Mrszcup/jetson-nano-baseboard/display.sch

## KiCad design display.sch (2021-12-20)

Schematic: display.sch

Parts:
C1, C2: C_4u7_0402; 0402-cap; MPN GRM155R61A475MEAAD
C26, C27, C73, C74, C75, C76, C77, C78, C79, C80: C_100n_0402; 0402-cap; MPN 0402X104K6R3CT
D4: 1N4148WS; SOD-323; MPN 1N4148WS
IC6: PCA9517ADP; MSOP-8; MPN PCA9517ADP
IC18: SON-15; PartSymbol TPD8S009DSMR
J1: 46756-1001; HDMI_Micro-D_Molex_46765-1x01; MPN 467651001
L8, L9: BLM18SG121TN1D; 0603; MPN BLM18SG121TN1D
M1: jetson-nano-connector; PartSymbol 2309413-1
R1, R2, R3, R4, R7, R8, R9, R10: R_5R6_0402; 0402-res; MPN ERJ2GEJ5R6X
R5, R6, R11, R37, R81, R83, R88: R_2k_0402; 0402-res; MPN CRCW04022K00FKED
R12, R82, R98, R99: R_0R_0402; 0402-res; MPN ERJ2GE0R00X
T1: BSS138APW; SC70-3; MPN BSS138PW
TP2, TP25, TP26, TP33, TP34, TP35, TP36: TP-R-1.5; MPN N/A
U6, U7: TPD4E05U06QDQARQ1; MPN TPD4E05U06QDQARQ1

Connections:
1V8_SYS: R88.1
3V3_SYS: C26.1, IC6.1 (VCCA), R11.1, R81.1
5V0_SYS: L9.1
DP_HDP: M1.88 (DP0_HPD)
EDP0_TX_N: M1.39 (DP0_TXD0_N)
EDP0_TX_P: M1.41 (DP0_TXD0_P)
EDP1_TX_N: M1.45 (DP0_TXD1_N)
EDP1_TX_P: M1.47 (DP0_TXD1_P)
EDP2_TX_N: M1.51 (DP0_TXD2_N)
EDP2_TX_P: M1.53 (DP0_TXD2_P)
EDP3_TX_N: M1.57 (DP0_TXD3_N)
EDP3_TX_P: M1.59 (DP0_TXD3_P)
EDP_AUX_N: M1.90 (DP0_AUX_N)
EDP_AUX_P: M1.92 (DP0_AUX_P)
GND: C1.1, C2.1, C26.2, C27.1, IC6.4 (GND), IC18.2 (GND), IC18.5 (GND), IC18.8 (GND), IC18.11 (GND), L8.1, R12.1, R37.2, R83.2, T1.2 (S), U6.3 (GND), U6.8 (GND), U7.3 (GND), U7.8 (GND)
HDMI_PWR: C27.2, D4.A, IC6.5 (EN), IC6.8 (VCCB), IC18.13 (VCC), IC18.15 (VCC), L9.2, R5.1, R6.1
HDMI_SHIELD: J1.4 (D2S), J1.7 (D1S), J1.10 (D0S), J1.13 (CKS), J1.SH, L8.2
M2_ALERT: M1.212 (GPIO10), TP2.1
unnamed: C1.2, C2.2, D4.C, J1.19 (+5V)
unnamed: IC6.2 (SCLA), R81.2, R98.1
unnamed: IC6.3 (SDAA), R11.2, R99.1
unnamed: R82.2, R83.1, T1.1 (G)
unnamed: U6.4 (IO3), U6.7 (IO3)
unnamed: U6.5 (IO4), U6.6 (IO4)
unnamed: U7.5 (IO4), U7.6 (IO4)
OTG_USB_VBUS: M1.87 (GPIO00)
TMDS_C1_CLK_N: C80.2, IC18.12 (D3-), R10.1
TMDS_C1_CLK_P: C78.2, IC18.10 (D3+), R9.1
TMDS_C1_D0_N: C79.2, IC18.9 (D2-), R8.1
TMDS_C1_D0_P: C76.2, IC18.7 (D2+), R7.1
TMDS_C1_D1_N: C77.2, IC18.6 (D1-), R4.1
TMDS_C1_D1_P: C75.2, IC18.4 (D1+), R3.1
TMDS_C1_D2_N: C74.2, IC18.3 (D0-), R2.1
TMDS_C1_D2_P: C73.2, IC18.1 (D0+), R1.1
TMDS_CEC: M1.94 (HDMI_CEC), TP26.1
TMDS_CEC_GND: J1.16 (GND), R12.2, U6.2 (IO2), U6.9 (IO2)
TMDS_CEC_IN: J1.15 (CEC), R37.1, U6.1 (IO1), U6.10 (IO1)
TMDS_CLK_C_N: J1.14 (CK-), R10.2
TMDS_CLK_C_P: J1.12 (CK+), R9.2
TMDS_CLK_N: C80.1, M1.81 (DP1_TXD3_N)
TMDS_CLK_P: C78.1, M1.83 (DP1_TXD3_P)
TMDS_D0_C_N: J1.11 (D0-), R8.2
TMDS_D0_C_P: J1.9 (D0+), R7.2
TMDS_D0_N: C79.1, M1.75 (DP1_TXD2_N)
TMDS_D0_P: C76.1, M1.77 (DP1_TXD2_P)
TMDS_D1_C_N: J1.8 (D1-), R4.2
TMDS_D1_C_P: J1.6 (D1+), R3.2
TMDS_D1_N: C77.1, M1.69 (DP1_TXD1_N)
TMDS_D1_P: C75.1, M1.71 (DP1_TXD1_P)
TMDS_D2_C_N: J1.5 (D2-), R2.2
TMDS_D2_C_P: J1.3 (D2+), R1.2
TMDS_D2_N: C74.1, M1.63 (DP1_TXD0_N)
TMDS_D2_P: C73.1, M1.65 (DP1_TXD0_P)
TMDS_HPD: M1.96 (DP1_HPD), R88.2, T1.3 (D), TP25.1
TMDS_HPD_IN: J1.1 (HPD/HEAC-), R82.1, U7.4 (IO3), U7.7 (IO3)
TMDS_SCL: M1.100 (DP1_AUX_P), R98.2, TP33.1
TMDS_SCL_5V0: IC6.7 (SCLB), J1.17 (SCL), R5.2, U7.2 (IO2), U7.9 (IO2)
TMDS_SDA: M1.98 (DP1_AUX_N), R99.2, TP34.1
TMDS_SDA_5V0: IC6.6 (SDAB), J1.18 (SDA), R6.2, U7.1 (IO1), U7.10 (IO1)
USR_BUTTON: M1.218 (GPIO12), TP36.1
USR_LED: M1.206 (GPIO07), TP35.1

Notes on the sheet:
Text
Display
1V8
HDMI Interface
DDC/HPD
3V3
5V0
