Mrszcup/jetson-nano-baseboard/id-serial.sch

## KiCad design id-serial.sch (2021-12-31)

Schematic: id-serial.sch

Parts:
C36: C_100n_0402; 0402-cap; MPN 0402X104K6R3CT
D15: diode; SOD-323; MPN 1N4148WS
IC17: AT24CS01-ST; SOT23-5; MPN AT24CS01-ST
R132: R_0R_0402; 0402-res; MPN ERJ2GE0R00X
TP30: TC2030; MPN TC2030

Connections:
3V3_SYS: C36.2, D15.A
EEPROM_PWR: D15.C, IC17.4 (VCC), TP30.1 (VCC/VCCIO)
GEN0_SCL: IC17.1 (SCL), TP30.4 (TXD/TCLK)
GEN0_SDA: IC17.3 (SDA), TP30.3 (RXD/TDI), TP30.6 (RTS/TDO)
GND: C36.1, IC17.2 (GND), TP30.5 (GND)
unnamed: R132.2, TP30.2 (CTS/TMS)
SN_WP: IC17.5 (WP), R132.1

Notes on the sheet:
Text
EEPROM with Unique ID
0x58h - SN
I2C address:
0x50h - memory
ID serial
