Mrszcup/jetson-nano-baseboard/interfaces.sch

## KiCad design interfaces.sch (2021-12-21)

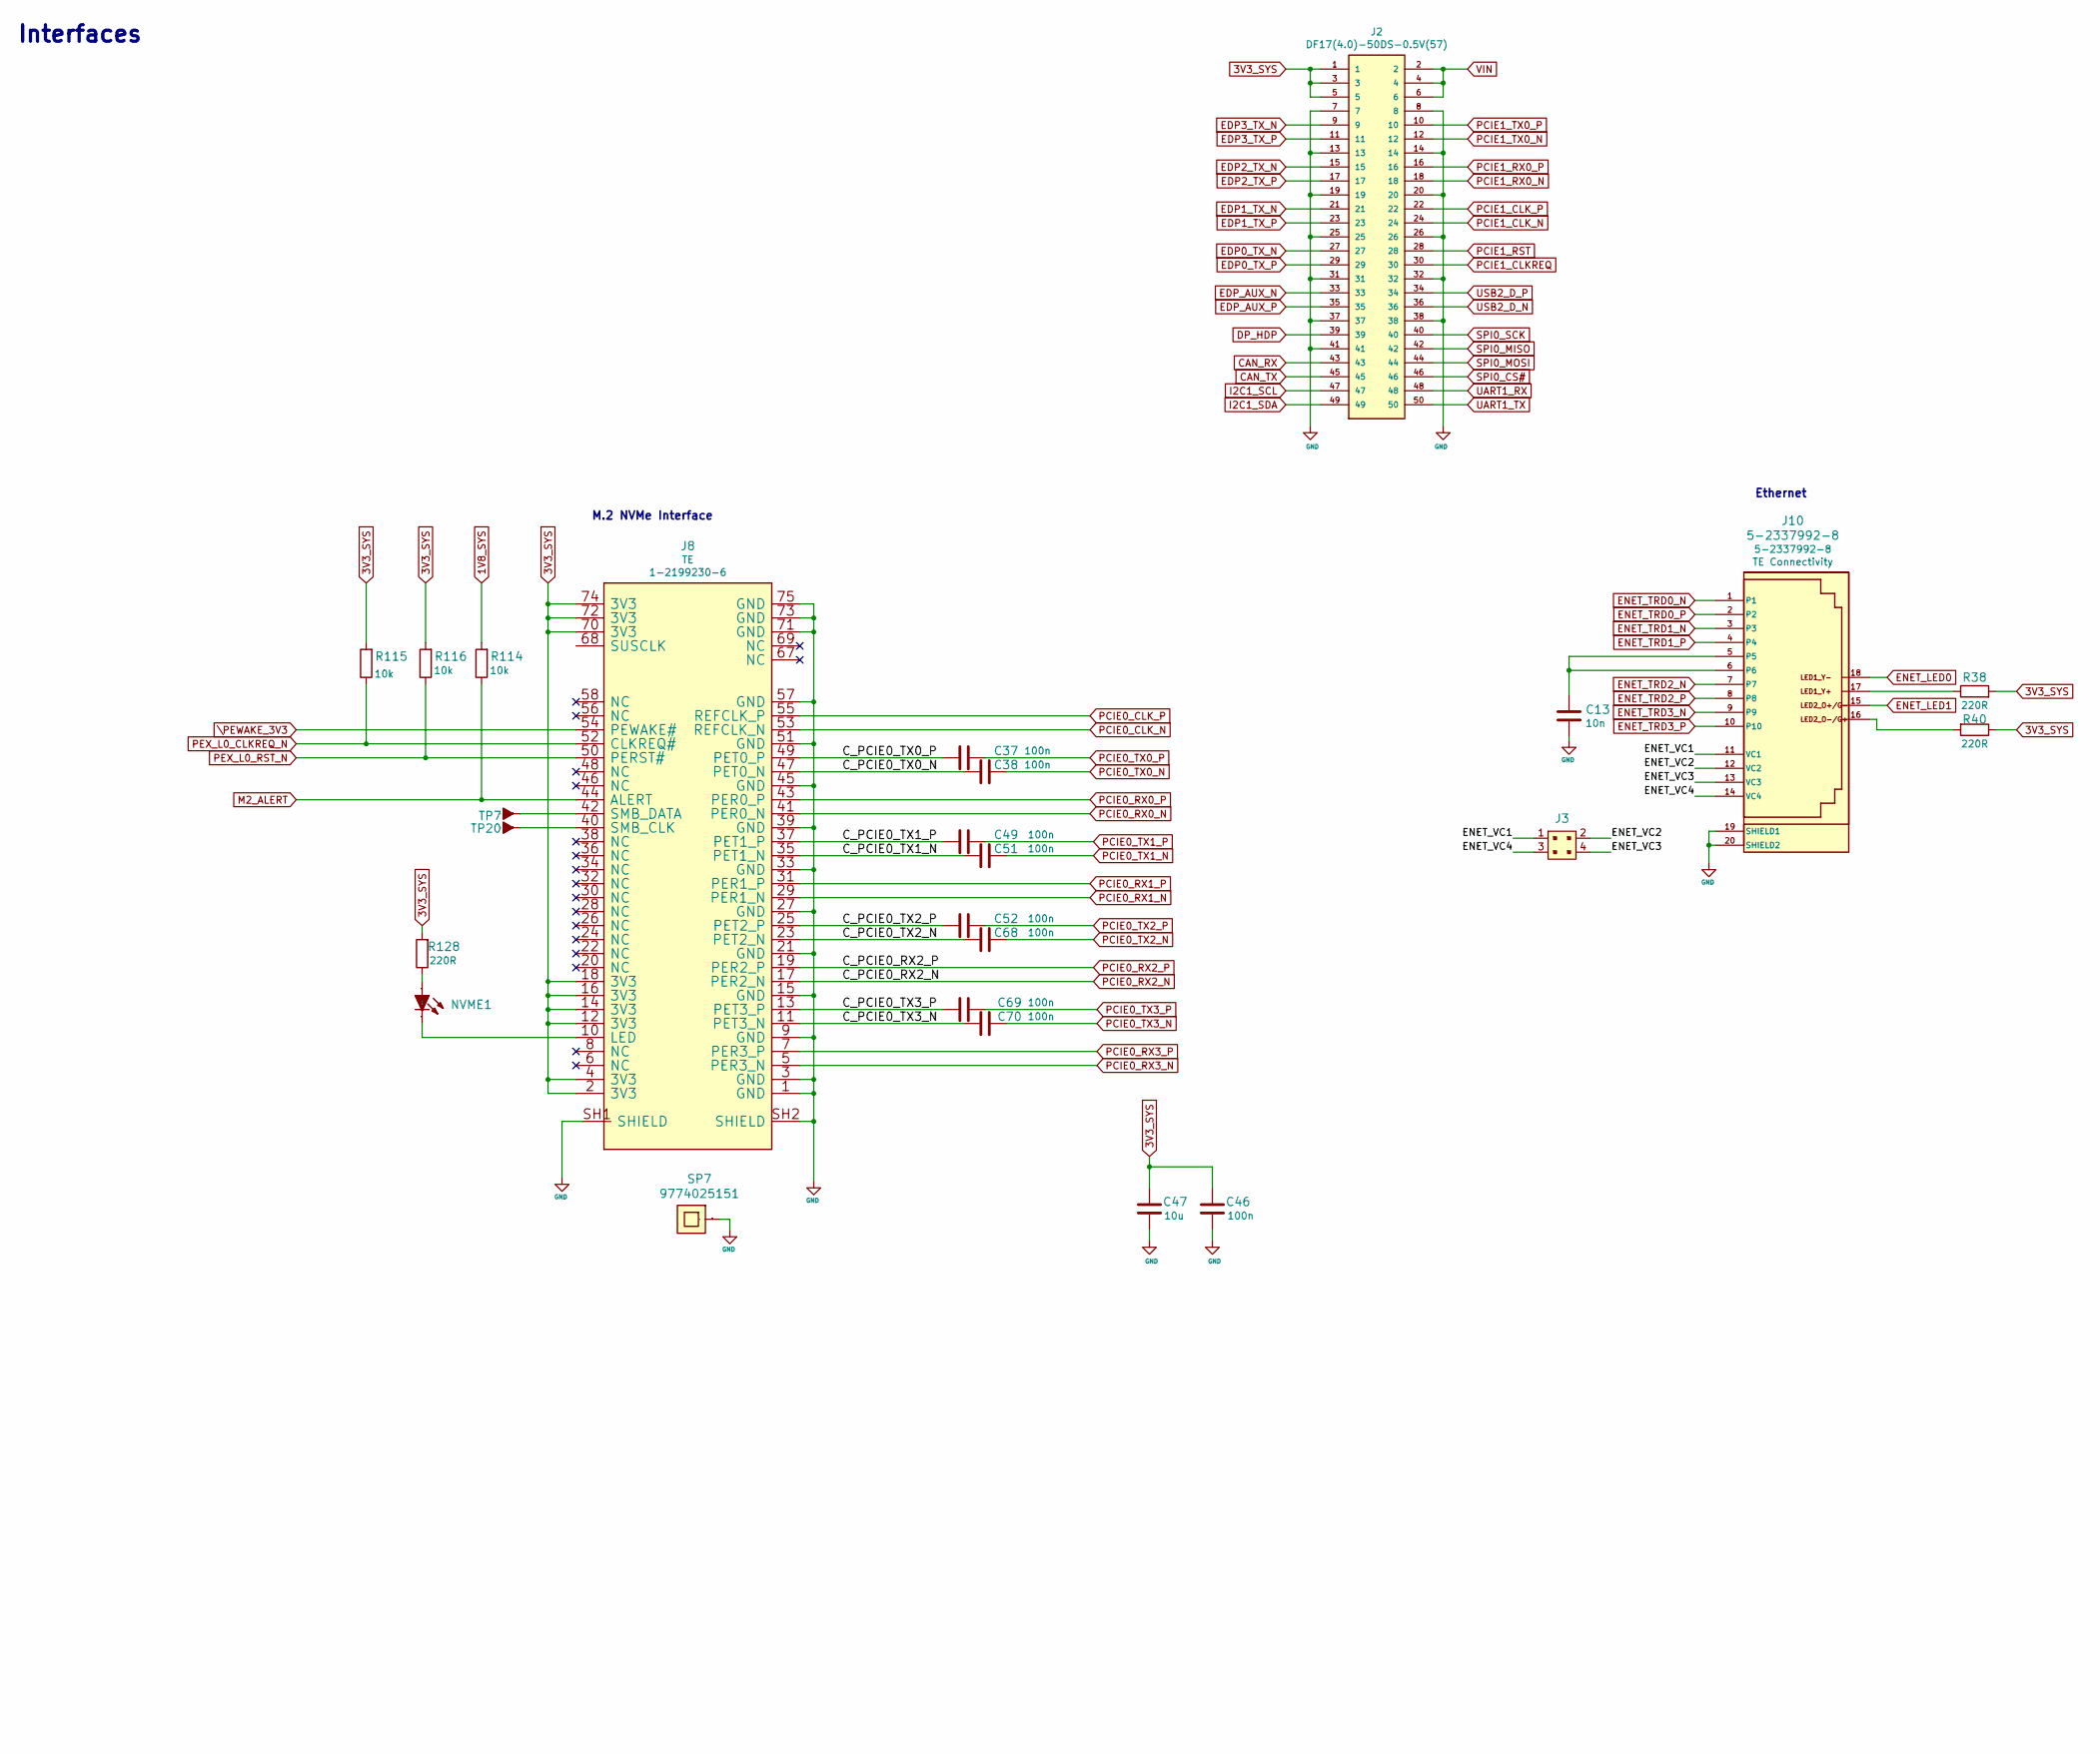
[picture p3: schematic interfaces.sch, part in row 1, column 1]

Parts:
C13: C_10n_0402; 0402-cap; MPN 04025G103ZAT2A
C37, C38, C46, C49, C51, C52, C68, C69, C70: C_100n_0402; 0402-cap; MPN 0402X104K6R3CT
C47: C_10u_0603; 0603-cap; MPN GRM188R61A106KE69D
J2: DF17(4.0)-50DS-0.5V(57); HRS_DF17(4.0)-50DS-0.5V(57); MPN DF17(4.0)-50DS-0.5V(57)
J3: 62100421821; 621304242921; MPN 62100421821
J8: 1-2199230-6; MPN 1-2199230-6
J10: 5-2337992-8; MPN 5-2337992-8
NVME1: LED0603; MPN KPT-1608SGC
R38, R40, R128: R_220R_0402; 0402-res; MPN ERJ2GEJ221X
R114, R115, R116: R_10k_0402; 0402-res; MPN CRCW040210K0FKEDHP
SP7: 9774025151; MPN 9774025151
TP7, TP20: TP-R-1.5; MPN N/A

Connections:
1V8_SYS: R114.2
3V3_SYS: C46.2, C47.2, J2.1, J2.3, J2.5, J8.2 (3V3), J8.4 (3V3), J8.12 (3V3), J8.14 (3V3), J8.16 (3V3), J8.18 (3V3), J8.70 (3V3), J8.72 (3V3), J8.74 (3V3), R38.2, R40.1, R115.2, R116.2, R128.2
CAN_RX: J2.43
CAN_TX: J2.45
C_PCIE0_TX0_N: C38.1, J8.47 (PET0_N)
C_PCIE0_TX0_P: C37.1, J8.49 (PET0_P)
C_PCIE0_TX1_N: C51.1, J8.35 (PET1_N)
C_PCIE0_TX1_P: C49.1, J8.37 (PET1_P)
C_PCIE0_TX2_N: C68.1, J8.23 (PET2_N)
C_PCIE0_TX2_P: C52.1, J8.25 (PET2_P)
C_PCIE0_TX3_N: C70.1, J8.11 (PET3_N)
C_PCIE0_TX3_P: C69.1, J8.13 (PET3_P)
DP_HDP: J2.39
EDP0_TX_N: J2.27
EDP0_TX_P: J2.29
EDP1_TX_N: J2.21
EDP1_TX_P: J2.23
EDP2_TX_N: J2.15
EDP2_TX_P: J2.17
EDP3_TX_N: J2.9
EDP3_TX_P: J2.11
EDP_AUX_N: J2.33
EDP_AUX_P: J2.35
ENET_LED0: J10.18
ENET_LED1: J10.15
ENET_TRD0_N: J10.1
ENET_TRD0_P: J10.2
ENET_TRD1_N: J10.3
ENET_TRD1_P: J10.4
ENET_TRD2_N: J10.7
ENET_TRD2_P: J10.8
ENET_TRD3_N: J10.9
ENET_TRD3_P: J10.10
ENET_VC1: J3.1, J10.11 (VC1)
ENET_VC2: J3.2, J10.12 (VC2)
ENET_VC3: J3.4, J10.13 (VC3)
ENET_VC4: J3.3, J10.14 (VC4)
GND: C13.2, C46.1, C47.1, J2.7, J2.8, J2.13, J2.14, J2.19, J2.20, J2.25, J2.26, J2.31, J2.32, J2.37, J2.38, J2.41, J8.1 (GND), J8.3 (GND), J8.9 (GND), J8.15 (GND), J8.21 (GND), J8.27 (GND), J8.33 (GND), J8.39 (GND), J8.45 (GND), J8.51 (GND), J8.57 (GND), J8.71 (GND), J8.73 (GND), J8.75 (GND), J8.SH1 (SHIELD), J8.SH2 (SHIELD), J10.19 (SHIELD1), J10.20 (SHIELD2), SP7.1
I2C1_SCL: J2.47
I2C1_SDA: J2.49
M2_ALERT: J8.44 (ALERT), R114.1
unnamed: C13.1, J10.5, J10.6
unnamed: J8.10 (LED), NVME1.K
unnamed: J8.40 (SMB_CLK), TP20.1
unnamed: J8.42 (SMB_DATA), TP7.1
unnamed: J10.16, R40.2
unnamed: J10.17, R38.1
unnamed: NVME1.A, R128.1
PCIE0_CLK_N: J8.53 (REFCLK_N)
PCIE0_CLK_P: J8.55 (REFCLK_P)
PCIE0_RX0_N: J8.41 (PER0_N)
PCIE0_RX0_P: J8.43 (PER0_P)
PCIE0_RX1_N: J8.29 (PER1_N)
PCIE0_RX1_P: J8.31 (PER1_P)
PCIE0_RX2_N: J8.17 (PER2_N)
PCIE0_RX2_P: J8.19 (PER2_P)
PCIE0_RX3_N: J8.5 (PER3_N)
PCIE0_RX3_P: J8.7 (PER3_P)
PCIE0_TX0_N: C38.2
PCIE0_TX0_P: C37.2
PCIE0_TX1_N: C51.2
PCIE0_TX1_P: C49.2
PCIE0_TX2_N: C68.2
PCIE0_TX2_P: C52.2
PCIE0_TX3_N: C70.2
PCIE0_TX3_P: C69.2
PCIE1_CLKREQ: J2.30
PCIE1_CLK_N: J2.24
PCIE1_CLK_P: J2.22
PCIE1_RST: J2.28
PCIE1_RX0_N: J2.18
PCIE1_RX0_P: J2.16
PCIE1_TX0_N: J2.12
PCIE1_TX0_P: J2.10
PEX_L0_CLKREQ_N: J8.52 (CLKREQ#), R115.1
PEX_L0_RST_N: J8.50 (PERST#), R116.1
SPI0_CS#: J2.46
SPI0_MISO: J2.42
SPI0_MOSI: J2.44
SPI0_SCK: J2.40
UART1_RX: J2.48
UART1_TX: J2.50
USB2_D_N: J2.36
USB2_D_P: J2.34
VIN: J2.2, J2.4, J2.6
\PEWAKE_3V3: J8.54 (PEWAKE#)

Notes on the sheet:
Text
Ethernet
M.2 NVMe Interface
Interfaces
