Mrszcup/jetson-nano-baseboard/jetson-nano-baseboard.sch

## KiCad design jetson-nano-baseboard.sch (2021-10-04)

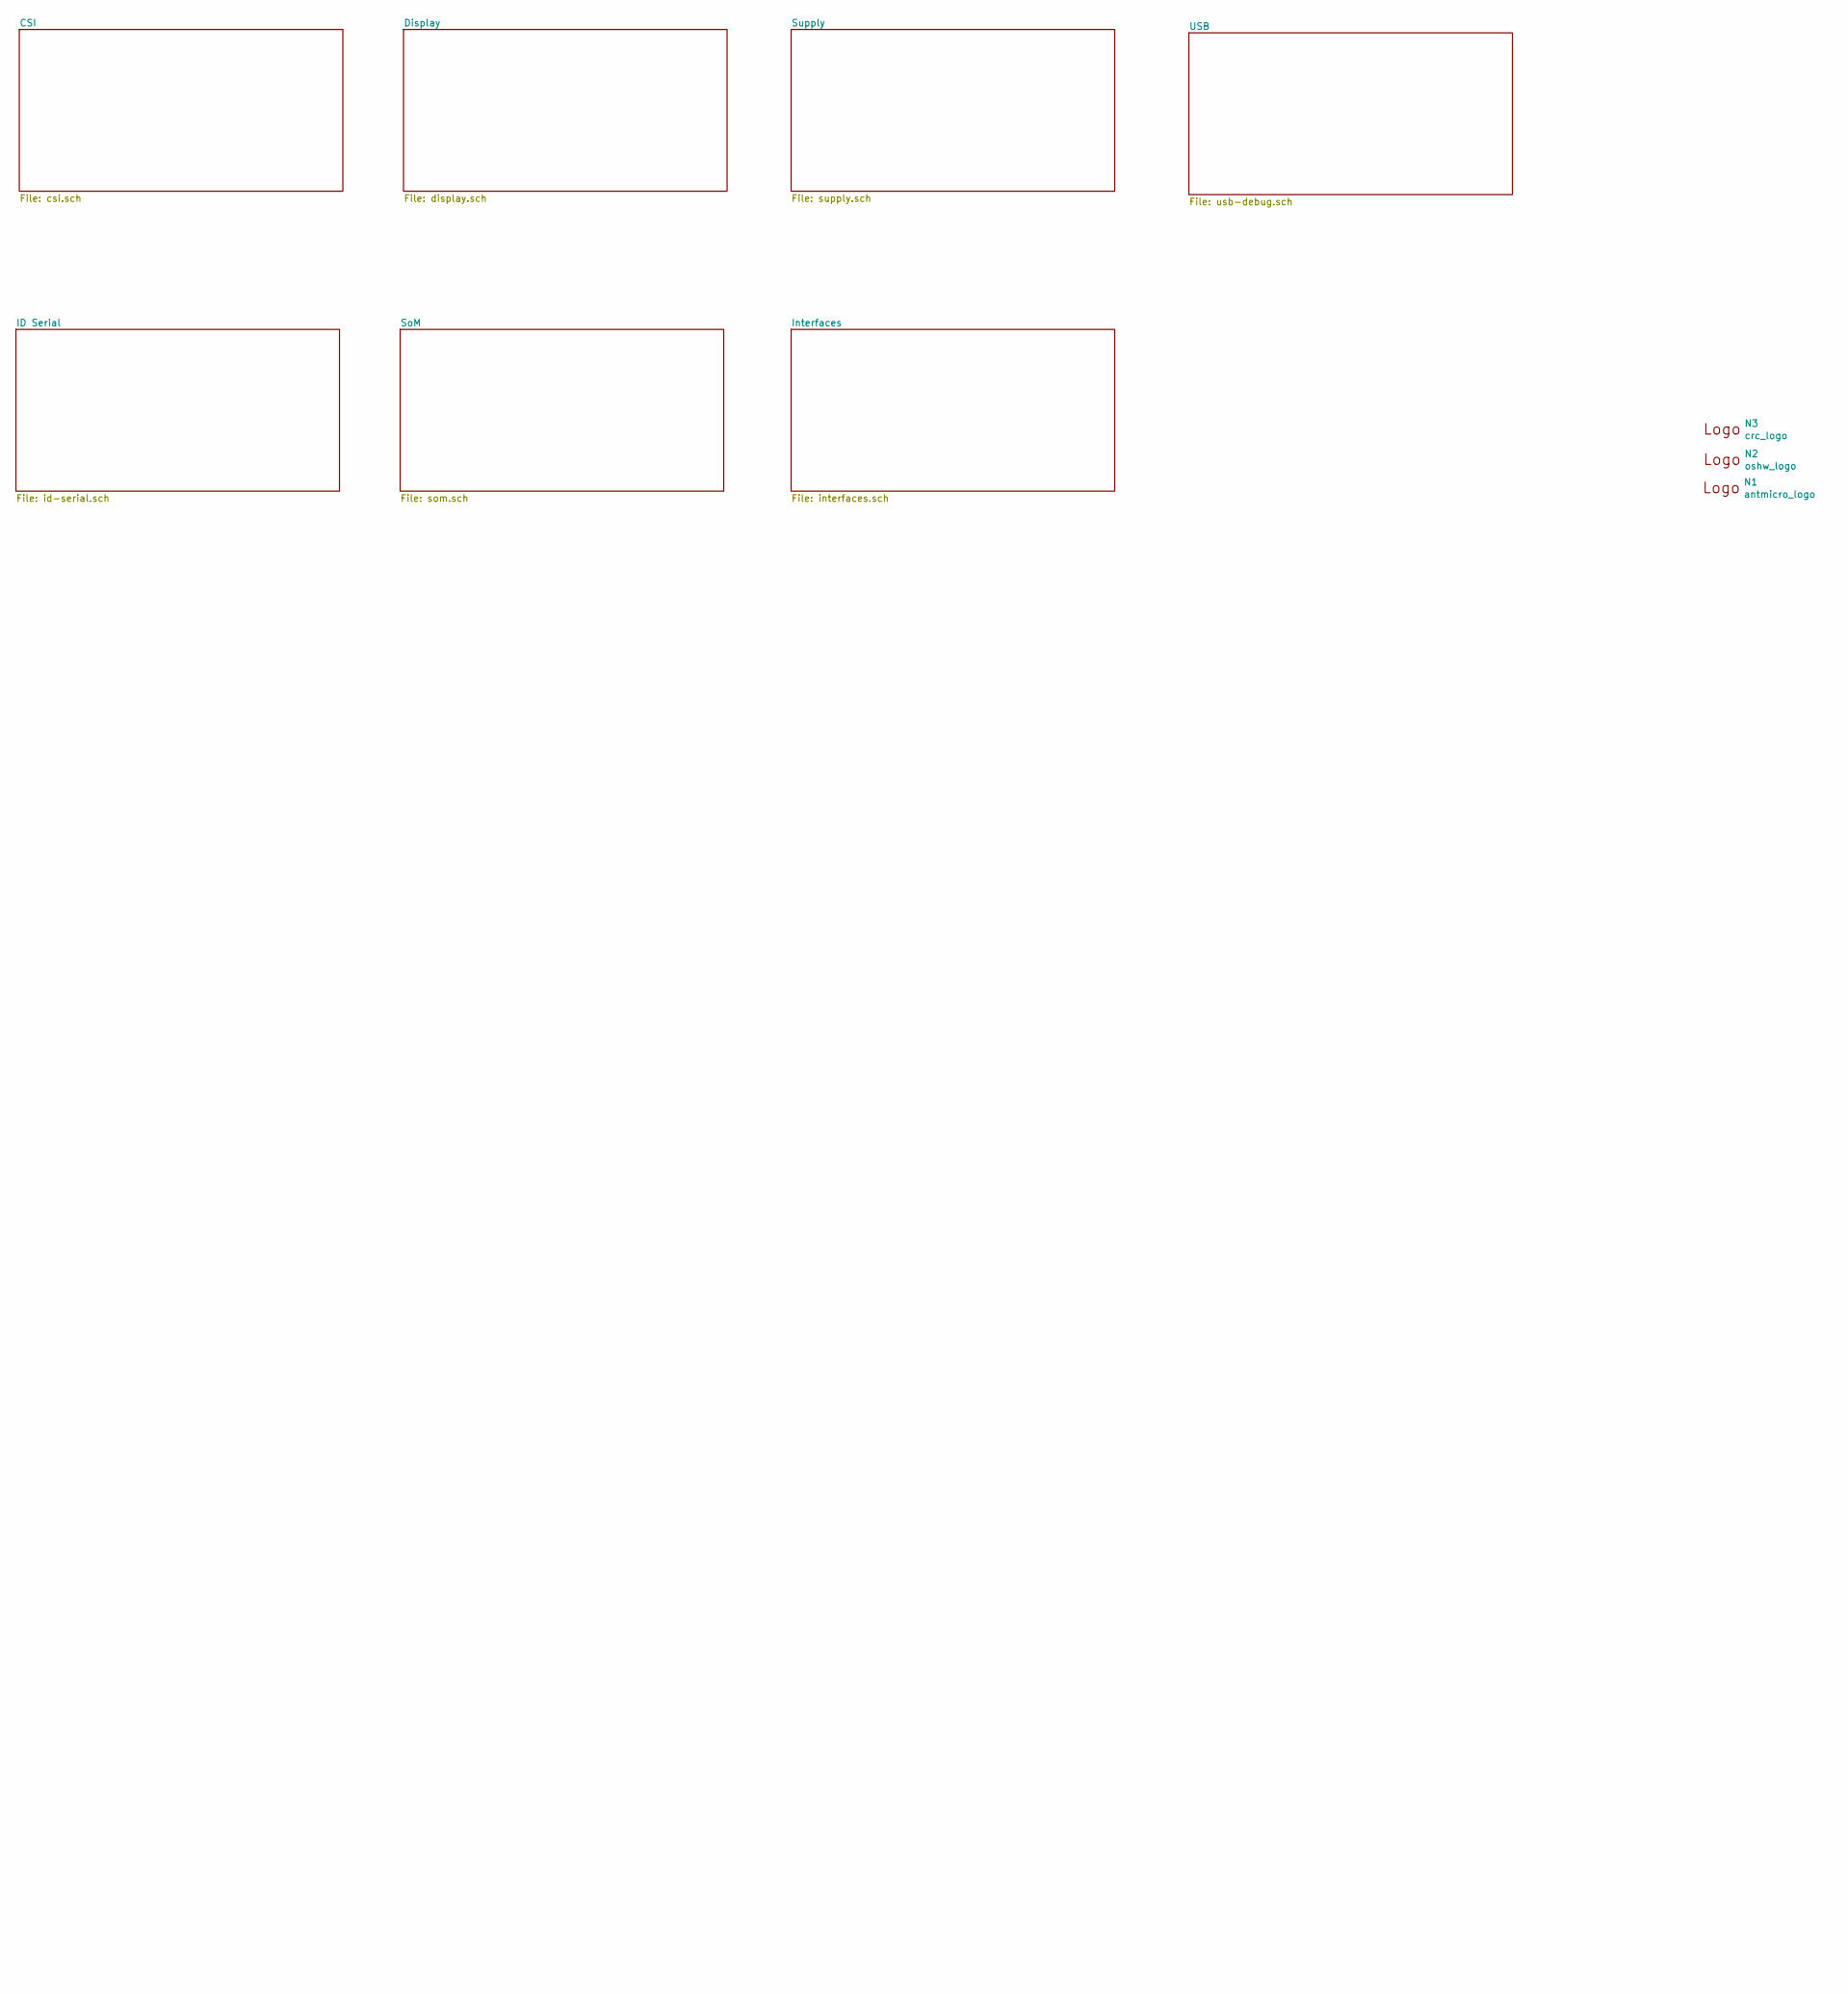
[picture p4: schematic jetson-nano-baseboard.sch, part in row 1, column 1]

Parts:
N1: antmicro_logo; antmicro-logo_scaled_15mm
N2: oshw_logo; oshw-logo
N3: crc_logo; CRC_logo_15mm

Notes on the sheet:
Text
