Mrszcup/jetson-nano-baseboard/som.sch

## KiCad design som.sch (2021-12-21)

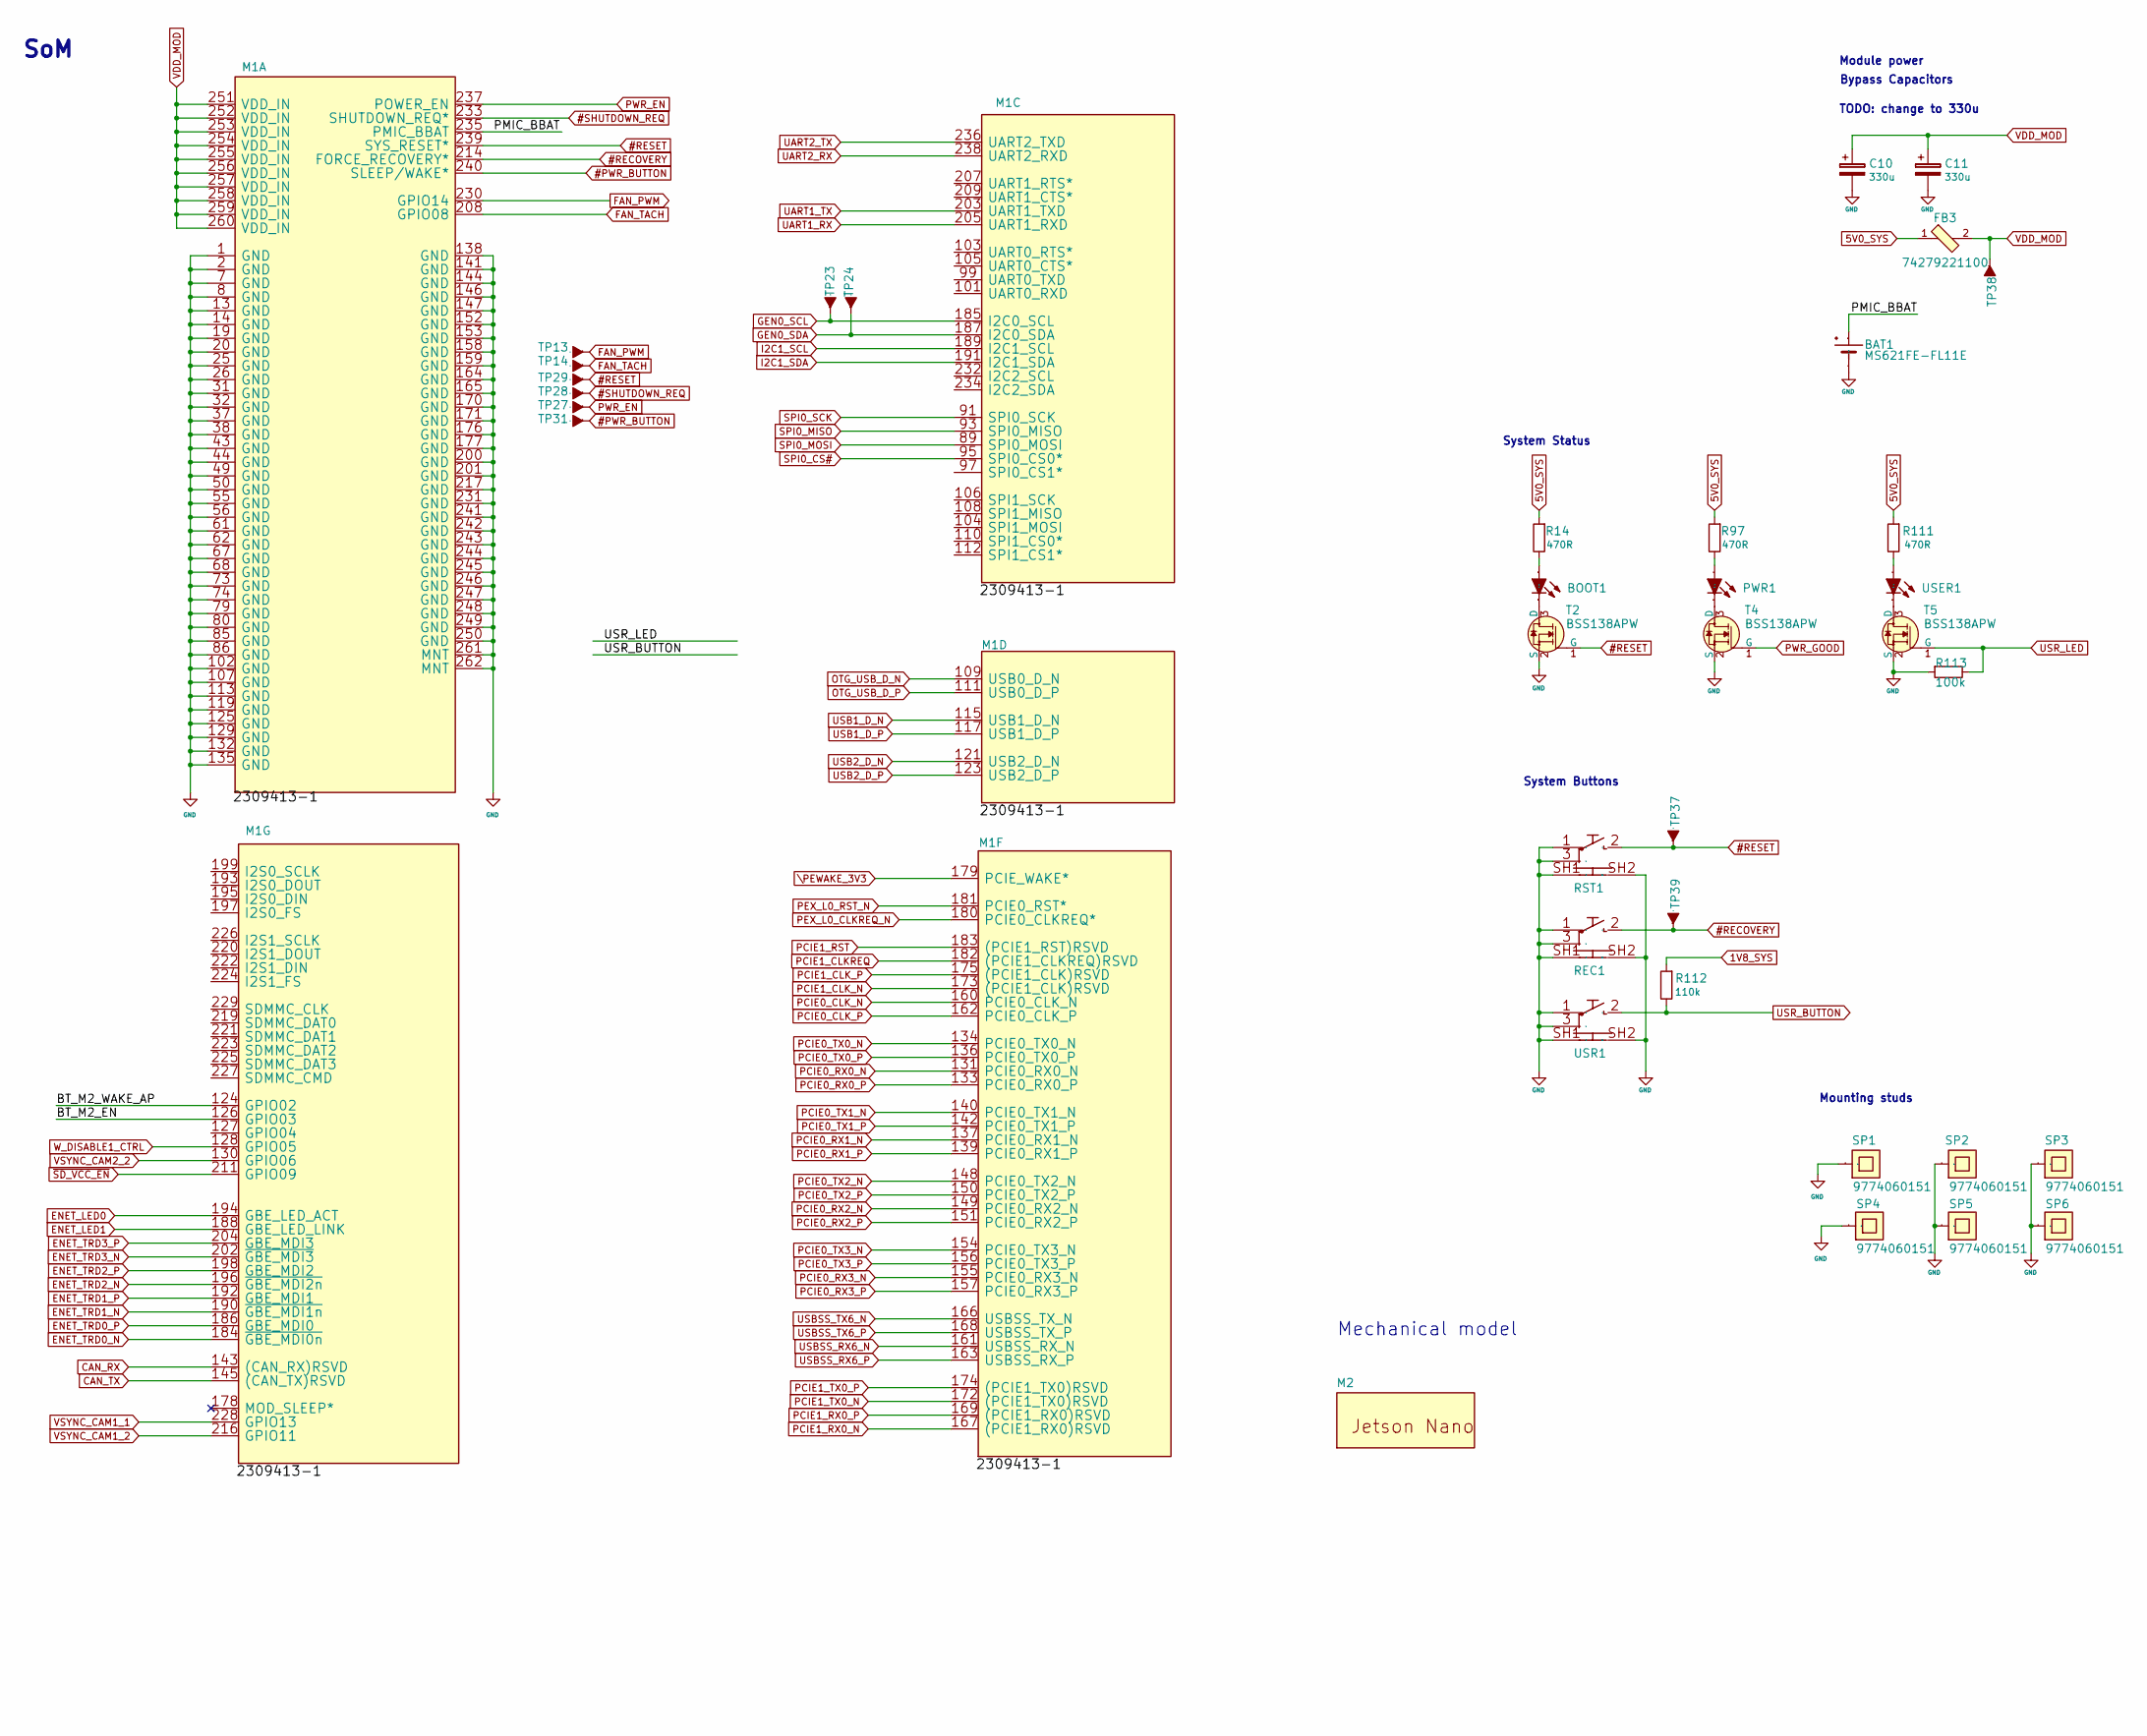
[picture p5: schematic som.sch, part in row 1, column 1]

Parts:
BAT1: MS621FE-FL11E; MPN MS621FE-FL11E
BOOT1: LED0603; MPN KPT-1608SGC
C10, C11: C_330u_KEMET_B; KEMET_B; MPN T520B337M006ATE040
FB3: 74279221100; 1206-res; MPN 74279221100
M1, M1_4: jetson-nano-connector; PartSymbol 2309413-1
M2: jetson-nano-module; MPN 900-13448-0020-000
PWR1: LED0603; MPN KPT-1608SGC
R14, R97, R111: R_470R_0402; 0402-res; MPN CRCW0402470RFKED
R112: R_110k_0603; 0603-res; MPN CPF0603B110KE1
R113: 100k; 0402; MPN ERJ2GE0R00X
REC1: TL3340AF160QG; PartSymbol TL3340AF160QG
RST1: TL3340AF160QG; PartSymbol TL3340AF160QG
SP1, SP2, SP3, SP4, SP5, SP6: 9774060151; M2.5-6mm; MPN 9774060151
T2, T4, T5: BSS138APW; SC70-3; MPN BSS138PW
TP13, TP14, TP23, TP24, TP27, TP28, TP29, TP31, TP37, TP38, TP39: TP-R-1.5; MPN N/A
USER1: LED0603; MPN KPT-1608SGC
USR1: TL3340AF160QG; PartSymbol TL3340AF160QG

Connections:
1V8_SYS: R112.2
5V0_SYS: FB3.1, R14.2, R97.2, R111.2
#PWR_BUTTON: M1.240 (SLEEP/WAKE*), TP31.1
#RECOVERY: M1.214 (FORCE_RECOVERY*), REC1.2, TP39.1
#RESET: M1.239 (SYS_RESET*), RST1.2, T2.1 (G), TP29.1, TP37.1
#SHUTDOWN_REQ: M1.233 (SHUTDOWN_REQ*), TP28.1
BT_M2_EN: M1.126 (GPIO03)
BT_M2_WAKE_AP: M1.124 (GPIO02)
CAN_RX: M1.143 ((CAN_RX)RSVD)
CAN_TX: M1.145 ((CAN_TX)RSVD)
ENET_LED0: M1.194 (GBE_LED_ACT)
ENET_LED1: M1.188 (GBE_LED_LINK)
ENET_TRD0_N: M1.184 (~GBE_MDI0n)
ENET_TRD0_P: M1.186 (GBE_MDI0)
ENET_TRD1_N: M1.190 (~GBE_MDI1n)
ENET_TRD1_P: M1.192 (GBE_MDI1)
ENET_TRD2_N: M1.196 (~GBE_MDI2n)
ENET_TRD2_P: M1.198 (GBE_MDI2)
ENET_TRD3_N: M1.202 (~GBE_MDI3)
ENET_TRD3_P: M1.204 (GBE_MDI3)
FAN_PWM: M1.230 (GPIO14), TP13.1
FAN_TACH: M1.208 (GPIO08), TP14.1
GEN0_SCL: M1_4.185 (I2C0_SCL), TP23.1
GEN0_SDA: M1_4.187 (I2C0_SDA), TP24.1
GND: BAT1.-, C10.2, C11.2, M1.1 (GND), M1.2 (GND), M1.7 (GND), M1.8 (GND), M1.13 (GND), M1.14 (GND), M1.19 (GND), M1.20 (GND), M1.25 (GND), M1.26 (GND), M1.31 (GND), M1.32 (GND), M1.37 (GND), M1.38 (GND), M1.43 (GND), M1.44 (GND), M1.49 (GND), M1.50 (GND), M1.55 (GND), M1.56 (GND), M1.61 (GND), M1.62 (GND), M1.67 (GND), M1.68 (GND), M1.73 (GND), M1.74 (GND), M1.79 (GND), M1.80 (GND), M1.85 (GND), M1.86 (GND), M1.102 (GND), M1.107 (GND), M1.113 (GND), M1.119 (GND), M1.125 (GND), M1.129 (GND), M1.132 (GND), M1.135 (GND), M1.138 (GND), M1.141 (GND), M1.144 (GND), M1.146 (GND), M1.147 (GND), M1.152 (GND), M1.153 (GND), M1.158 (GND), M1.159 (GND), M1.164 (GND), M1.165 (GND), M1.170 (GND), M1.171 (GND), M1.176 (GND), M1.177 (GND), M1.200 (GND), M1.201 (GND), M1.217 (GND), M1.231 (GND), M1.241 (GND), M1.242 (GND), M1.243 (GND), M1.244 (GND), M1.245 (GND), M1.246 (GND), M1.247 (GND), M1.248 (GND), M1.249 (GND), M1.250 (GND), M1.261 (MNT), M1.262 (MNT), R113.2, REC1.1, REC1.3, REC1.SH1, REC1.SH2, RST1.1, RST1.3, RST1.SH1, RST1.SH2, SP1.1, SP2.1, SP3.1, SP4.1, SP5.1, SP6.1, T2.2 (S), T4.2 (S), T5.2 (S), USR1.1, USR1.3, USR1.SH1, USR1.SH2
I2C1_SCL: M1_4.189 (I2C1_SCL)
I2C1_SDA: M1_4.191 (I2C1_SDA)
unnamed: BOOT1.A, R14.1
unnamed: BOOT1.K, T2.3 (D)
unnamed: PWR1.A, R97.1
unnamed: PWR1.K, T4.3 (D)
unnamed: R111.1, USER1.A
unnamed: T5.3 (D), USER1.K
OTG_USB_D_N: M1.109 (USB0_D_N)
OTG_USB_D_P: M1.111 (USB0_D_P)
PCIE0_CLK_N: M1.160 (PCIE0_CLK_N)
PCIE0_CLK_P: M1.162 (PCIE0_CLK_P)
PCIE0_RX0_N: M1.131 (PCIE0_RX0_N)
PCIE0_RX0_P: M1.133 (PCIE0_RX0_P)
PCIE0_RX1_N: M1.137 (PCIE0_RX1_N)
PCIE0_RX1_P: M1.139 (PCIE0_RX1_P)
PCIE0_RX2_N: M1.149 (PCIE0_RX2_N)
PCIE0_RX2_P: M1.151 (PCIE0_RX2_P)
PCIE0_RX3_N: M1.155 (PCIE0_RX3_N)
PCIE0_RX3_P: M1.157 (PCIE0_RX3_P)
PCIE0_TX0_N: M1.134 (PCIE0_TX0_N)
PCIE0_TX0_P: M1.136 (PCIE0_TX0_P)
PCIE0_TX1_N: M1.140 (PCIE0_TX1_N)
PCIE0_TX1_P: M1.142 (PCIE0_TX1_P)
PCIE0_TX2_N: M1.148 (PCIE0_TX2_N)
PCIE0_TX2_P: M1.150 (PCIE0_TX2_P)
PCIE0_TX3_N: M1.154 (PCIE0_TX3_N)
PCIE0_TX3_P: M1.156 (PCIE0_TX3_P)
PCIE1_CLKREQ: M1.182 ((PCIE1_CLKREQ)RSVD)
PCIE1_CLK_N: M1.173 ((PCIE1_CLK)RSVD)
PCIE1_CLK_P: M1.175 ((PCIE1_CLK)RSVD)
PCIE1_RST: M1.183 ((PCIE1_RST)RSVD)
PCIE1_RX0_N: M1.167 ((PCIE1_RX0)RSVD)
PCIE1_RX0_P: M1.169 ((PCIE1_RX0)RSVD)
PCIE1_TX0_N: M1.172 ((PCIE1_TX0)RSVD)
PCIE1_TX0_P: M1.174 ((PCIE1_TX0)RSVD)
PEX_L0_CLKREQ_N: M1.180 (PCIE0_CLKREQ*)
PEX_L0_RST_N: M1.181 (PCIE0_RST*)
PMIC_BBAT: BAT1.+, M1.235 (PMIC_BBAT)
PWR_EN: M1.237 (POWER_EN), TP27.1
PWR_GOOD: T4.1 (G)
SPI0_CS#: M1_4.95 (SPI0_CS0*)
SPI0_MISO: M1_4.93 (SPI0_MISO)
SPI0_MOSI: M1_4.89 (SPI0_MOSI)
SPI0_SCK: M1_4.91 (SPI0_SCK)
UART1_RX: M1_4.205 (UART1_RXD)
UART1_TX: M1_4.203 (UART1_TXD)
UART2_RX: M1_4.238 (UART2_RXD)
UART2_TX: M1_4.236 (UART2_TXD)
USB1_D_N: M1.115 (USB1_D_N)
USB1_D_P: M1.117 (USB1_D_P)
USB2_D_N: M1.121 (USB2_D_N)
USB2_D_P: M1.123 (USB2_D_P)
USBSS_RX6_N: M1.161 (USBSS_RX_N)
USBSS_RX6_P: M1.163 (USBSS_RX_P)
USBSS_TX6_N: M1.166 (USBSS_TX_N)
USBSS_TX6_P: M1.168 (USBSS_TX_P)
USR_BUTTON: R112.1, USR1.2
USR_LED: R113.1, T5.1 (G)
VDD_MOD: C10.1, C11.1, FB3.2, M1.251 (VDD_IN), M1.252 (VDD_IN), M1.253 (VDD_IN), M1.254 (VDD_IN), M1.255 (VDD_IN), M1.256 (VDD_IN), M1.257 (VDD_IN), M1.258 (VDD_IN), M1.259 (VDD_IN), M1.260 (VDD_IN), TP38.1
VSYNC_CAM1_1: M1.228 (GPIO13)
VSYNC_CAM1_2: M1.216 (GPIO11)
VSYNC_CAM2_2: M1.130 (GPIO06)
W_DISABLE1_CTRL: M1.128 (GPIO05)
\PEWAKE_3V3: M1.179 (PCIE_WAKE*)
~SD_VCC_EN~: M1.211 (GPIO09)

Notes on the sheet:
Mechanical model
Mounting studs
Bypass Capacitors
System Buttons
System Status
Module power
Text
SoM
TODO: change to 330u
