Mrszcup/jetson-nano-baseboard/supply.sch

## KiCad design supply.sch (2021-12-19)

Schematic: supply.sch

Parts:
C16, C18, C19, C21: C_10u_1206_50V; 1206-cap; MPN C3216X7R1H106K160AE
C17, C20: C_47u_0805; 0805-cap; MPN C0805C476M9PACTU
C22, C24: C_6p_0402; 0402-cap; MPN 0402N6R0D500CT
C23, C25: C_10u_0805; 0805-cap; MPN 160R15X106KV4E
C41: C_47n_0402; 0402-cap; MPN MC0402X473K160CT
C60: C_2u2_0402; 0402-cap; MPN C1005X5R1A225K050BC
C63: C_10u_0603; 0603-cap; MPN GRM188R61A106KE69D
C65, C87, C88: C_1u_0402; 0402-cap; MPN C1005X6S1A105K050BC
C71, C89, C90: C_100n_0402; 0402-cap; MPN 0402X104K6R3CT
D13: 1N4148WS; SOD-323; MPN 1N4148WS
F1, F2: 04671.25NR; 0603-Fuse-Littelfuse-0467; MPN 04671.25NR
FB1, FB2: 74279221100; 1206-res; MPN 74279221100
IC4: TPS7A0518PDBVT; SOT-23-5; MPN TPS7A0518PDBVT
IC12: 74HC00PW; TSSOP-14; MPN 74HC00PW
IC13: SN74LVC1G126DCKR; R-PDSO-G5; MPN SN74LVC1G126DCKR
J4: DC_SOCKET; MPN MJ-179PH
J12: 533980471; Molex_PicoBlade_53398-0471_1x04-1MP_P1.25mm_Vertical; MPN 0533980471
L1: XFL4015-122MEC; MPN XFL4015-122MEC
L4: XEL4030-222MEC; Coilcraft-XEL4030; MPN XEL4030-222MEC
R16, R36, R39, R45, R87: R_1k_0402; 0402-res; MPN CR0402-FX-1001GLF
R44, R46, R95: R_10k_0402; 0402-res; MPN CRCW040210K0FKEDHP
R84, R86: R_200k_0402; 0402-res; MPN RC0402FR-07200KL
R85: R_470k_0402; 0402-res; MPN RC0402FR-07470KL
R92, R130: R_0R_0402; 0402-res; MPN ERJ2GE0R00X
R117: R_100k_0402; 0402-res; MPN CRCW0402100KFKEDHP
R118, R120: R_100k_1%_0402; 0402; MPN ERA-6AEB104V
R119: R_44k2_0402; 0402-res; MPN ERJ2RKF4422X
R121: R_24k9_0.1%_0402; 0402-res; MPN RT0402BRE0724K9L
T3: BSS138APW; SC70-3; MPN BSS138PW
TP16, TP17, TP40, TP42, TP44, TP47: TP-R-1.5; MPN N/A
U1, U2: LM62440-Q1; VQFN-14-HR; MPN LMQ62440BPPQRJRRQ1
U3: TXB0101DBVT; SOT-23-6; MPN TXB0101DBVT

Connections:
1V8_SYS: C65.1, IC4.5 (VOUT), R95.1, T3.1 (G), TP47.1, U3.1 (VCCA), U3.5 (OE)
3V3_EN: R44.1, U2.7 (EN)
3V3_FB: R45.2, R118.2, R119.1, U2.4 (FB)
3V3_FFC1: F1.2
3V3_FFC2: F2.1
3V3_R_C_BOOT: C89.2, U2.13 (RBOOT), U2.14 (CBOOT)
3V3_SW: C89.1, L1.2, U2.10 (SW)
3V3_SYS: C20.1, C24.1, C25.1, F1.1, F2.2, L1.1, R118.1, U2.1 (BIAS)
3V3_VCC: C87.1, U2.2 (VCC)
3V3_VIN: C19.1, C21.1, FB1.2, U2.8 (VIN1), U2.12 (VIN2)
5V0_SYS: C17.1, C22.1, C23.1, C60.1, C71.2, IC4.1 (VIN), IC12.14 (VCC), IC13.1 (OE), IC13.5 (VCC), J12.2, L4.2, R16.1, R36.1, R46.2, R84.2, R86.2, R117.1, R120.1, TP42.1, U1.1 (BIAS), U3.6 (VCCB)
5V_FB: R39.2, R120.2, R121.1, U1.4 (FB)
5V_R_C_BOOT: C90.2, U1.13 (RBOOT), U1.14 (CBOOT)
5V_SW: C90.1, L4.1, U1.10 (SW)
5V_VCC: C88.1, U1.2 (VCC)
5V_VIN: C16.1, C18.1, FB2.2, U1.7 (EN), U1.8 (VIN1), U1.12 (VIN2)
#RESET: R44.2, R92.2
#SHUTDOWN_REQ: IC12.4 (2A), R86.1
FAN_PMW_5V: J12.4, U3.4 (B)
FAN_PWM: U3.3 (A)
FAN_TACH: R95.2, T3.2 (S)
FAN_TACH_5V: J12.3, R46.1, T3.3 (D)
GND: C16.2, C17.2, C18.2, C19.2, C20.2, C21.2, C23.2, C25.2, C41.1, C60.2, C63.1, C65.2, C71.1, C87.2, C88.2, IC4.2 (GND), IC12.7 (GND), IC13.3 (GND), J4.2, J4.3, J12.1, R119.2, R121.2, TP17.1, TP44.1, U1.3 (AGND), U1.6 (MODE), U1.9 (PGND1), U1.11 (PGND2), U2.3 (AGND), U2.6 (MODE), U2.9 (PGND1), U2.11 (PGND2), U3.2 (GND)
unnamed: C22.2, R39.1
unnamed: C24.2, R45.1
unnamed: IC4.3 (EN), R92.1
unnamed: IC12.2 (1B), IC12.6 (~2Y), R16.2
unnamed: IC12.8 (~3Y), R130.2
unnamed: IC12.9 (3A), IC12.10 (3B), IC12.11 (~4Y)
PWR_EN: IC13.4 (Y), R130.1
PWR_GOOD: R87.1, R117.2, TP40.1, U1.5 (PGOOD)
Q: D13.C, IC12.3 (~1Y), IC12.5 (2B), R36.2, R85.1
QDEL: C63.2, D13.A, IC12.12 (4A), IC12.13 (4B), IC13.2 (A), R85.2, R87.2
VIN: FB1.1, FB2.1, J4.1, TP16.1
\~PWR_SET~: C41.2, IC12.1 (1A), R84.1

Notes on the sheet:
Text
Power input
9...36 VDC
5V DC/DC
Power sequencer
#PWR_RST
Power Supply
5V/4A
TODO: change into locking one
System 1V8
3V3 DC/DC
3V3/4A
FAN 5V
