Mrszcup/jetson-nano-baseboard/usb-debug.sch

## KiCad design usb-debug.sch (2021-12-20)

Schematic: usb-debug.sch

Parts:
C15, C29: C_47p_0402; 0402-cap; MPN C0402C470J5GACTU
C30, C33, C48, C50, C53, C54, C72: C_100n_0402; 0402-cap; MPN 0402X104K6R3CT
C31: 100u; 1206; Voltage 6.3V; MPN C1206C107M9PACTU
C32: C_10u_0402; 0402-cap; MPN GRM155R60J106ME44D
C34: C_47u_0805; 0805-cap; MPN C0805C476M9PACTU
C35: C_10u_0603; 0603-cap; MPN GRM188R61A106KE69D
C62: C_4u7_0402; 0402-cap; MPN GRM155R61A475MEAAD
C66: C_1u_0402; 0402-cap; MPN C1005X6S1A105K050BC
C67: C_2u2_0402; 0402-cap; MPN C1005X5R1A225K050BC
D17: 1N4148WS; SOD-323; MPN 1N4148WS
IC1: TPS7A0518PDBVT; SOT-23-5; MPN TPS7A0518PDBVT
IC5: QFN-32; PartNumber FT232RQ
IC7: HD3SS3220; RNH0030A; MPN HD3SS3220RNHT
IC16: AP22652W6-7; SOT-23-6
J5, J9, J11: 632723300011; WE_632723300011; MPN 632723300011
L2, L3: BLM18EG221SN1D; 0603; MPN BLM18EG221SN1D
LED1: LED0603; MPN KPT-1608SGC
Q1: PMV32UP; SOT-23s; MPN PMV32UP
R20, R41: R_22R_0402; 0402-res; MPN CRCW040222R0FKED
R42, R49, R56, R62, R63, R64, R65, R66, R68, R71, R102, R103, R104, R105, R106, R107, R108, R109, R110: R_0R_0402; 0402-res; MPN ERJ2GE0R00X
R43: R_470R_0402; 0402-res; MPN CRCW0402470RFKED
R47, R54, R72, R131: R_10k_0402; 0402-res; MPN CRCW040210K0FKEDHP
R50: 10k2; 0402; MPN CPF0402B10K2E1
R51: R_909k_0402; 0402-res; MPN ERJ2RKF9093X
R53, R67: R_200k_0402; 0402-res; MPN RC0402FR-07200KL
R55, R69, R70, R73: R_2k_0402; 0402-res; MPN CRCW04022K00FKED
R101: R_100k_0402; 0402-res; MPN CRCW0402100KFKEDHP
T6, T7: BSS138APW; SC70-3; MPN BSS138PW
TP18, TP19, TP21, TP32: TP-R-1.5; MPN N/A
U8, U9, U10, U11, U12, U13: TPD4E05U06QDQARQ1; MPN TPD4E05U06QDQARQ1

Connections:
1V8_DBG: C66.2, IC1.5 (VOUT), IC5.1 (VCCIO)
3V3_SYS: C33.1, IC7.8 (VCC33), R53.2, R69.1, R70.1
5V0_DBG: C67.2, C72.2, D17.C, IC1.1 (VIN), IC1.3 (EN), IC5.19 (VCC), L3.2
5V0_SYS: C32.1, C34.2, D17.A, IC7.30 (VDD5), IC16.1 (IN), Q1.2 (S), R42.1, R43.2, R47.2, R54.1, R55.1, R67.2, R71.1, R101.2
CC1: IC7.2 (CC1), R63.1, R66.2
CC2: IC7.1 (CC2), R64.1, R65.2
C_CC1: J11.A5 (CC1), R63.2, R64.2, U10.1 (IO1), U10.10 (IO1)
C_CC2: J11.B5 (CC2), R65.1, R66.1, U10.2 (IO2), U10.9 (IO2)
C_USBSS_RX1_N: J11.B10 (SSRXn1), R104.2, U11.1 (IO1), U11.10 (IO1)
C_USBSS_RX1_P: J11.B11 (SSRXp1), R106.2, U11.2 (IO2), U11.9 (IO2)
C_USBSS_RX2_N: J11.A10 (SSRXn2), R109.2, U13.5 (IO4), U13.6 (IO4)
C_USBSS_RX2_P: J11.A11 (SSRXp2), R110.2, U13.4 (IO3), U13.7 (IO3)
C_USBSS_RX6_N: IC7.10 (RXn), R108.2
C_USBSS_RX6_P: IC7.9 (RXp), R107.2
C_USBSS_TX1_N: C48.1, J11.A3 (SSTXn1), U11.5 (IO4), U11.6 (IO4)
C_USBSS_TX1_P: C50.1, J11.A2 (SSTXp1), U11.4 (IO3), U11.7 (IO3)
C_USBSS_TX2_N: C53.1, J11.B3 (SSTXn2), U13.2 (IO2), U13.9 (IO2)
C_USBSS_TX2_P: C54.1, J11.B2 (SSTXp2), U13.1 (IO1), U13.10 (IO1)
C_USBSS_TX6_N: IC7.7 (TXn), R105.2
C_USBSS_TX6_P: IC7.6 (TXp), R103.2
DBG_USB_D_N: C29.2, IC5.15 (USBDN), J9.A7 (Dn1), J9.B7 (Dn2), U12.1 (IO1), U12.10 (IO1)
DBG_USB_D_P: C15.2, IC5.14 (USBDP), J9.A6 (Dp1), J9.B6 (Dp2), U12.2 (IO2), U12.9 (IO2)
DBG_VBUS: J9.A4 (VBUS), J9.A9 (VBUS), J9.B4 (VBUS), J9.B9 (VBUS), L3.1
EN_MUX: IC7.12 (ENn_MUX), R56.2, R68.1
GND: C15.1, C29.1, C30.1, C31.1, C32.2, C33.2, C34.1, C35.1, C62.1, C66.1, C67.1, C72.1, IC1.2 (GND), IC5.4 (GND), IC5.17 (GND), IC5.20 (GND), IC5.24 (AGND), IC5.26 (TEST), IC7.13 (GND), IC7.28 (GND), IC7.31 (GND), IC16.2 (GND), IC16.7 (GND), J5.A1 (GND), J5.A12 (GND), J5.B1 (GND), J5.B12 (GND), J5.Shell (Shield), J9.A1 (GND), J9.A12 (GND), J9.B1 (GND), J9.B12 (GND), J11.A1 (GND), J11.A12 (GND), J11.B1 (GND), J11.B12 (GND), J11.Shell (Shield), R50.1, R56.1, R62.1, R73.2, R102.1, R131.1, T6.2 (S), T7.2 (S), U8.3 (GND), U8.8 (GND), U9.3 (GND), U9.8 (GND), U10.3 (GND), U10.8 (GND), U11.3 (GND), U11.8 (GND), U12.3 (GND), U12.8 (GND), U13.3 (GND), U13.8 (GND)
unnamed: C30.2, IC5.16 (3V3OUT)
unnamed: C31.2, IC16.6 (OUT), L2.1
unnamed: IC5.2 (RXD), R41.1
unnamed: IC5.30 (TXD), R20.1
unnamed: IC7.3 (CURRENT_MODE), R54.2
unnamed: IC7.4 (PORT), R55.2
unnamed: IC7.5 (VBUS_DET), R51.1
unnamed: IC7.11 (DIR), R53.1
unnamed: IC7.29 (ENn_CC), R62.2
unnamed: IC16.3 (EN), R47.1, R49.2, R102.2
unnamed: IC16.4 (~FLAG~), LED1.K
unnamed: IC16.5 (ILIM), R50.2
unnamed: J11.B8 (SBU2), TP19.1
unnamed: LED1.A, R43.1
unnamed: Q1.3 (D), T7.1 (G)
unnamed: R49.1, T7.3 (D)
unnamed: R72.2, R73.1, T6.1 (G)
unnamed: U8.4 (IO3), U8.7 (IO3)
unnamed: U8.5 (IO4), U8.6 (IO4)
unnamed: U9.4 (IO3), U9.7 (IO3)
unnamed: U9.5 (IO4), U9.6 (IO4)
unnamed: U10.4 (IO3), U10.7 (IO3)
unnamed: U10.5 (IO4), U10.6 (IO4)
unnamed: U12.4 (IO3), U12.7 (IO3)
unnamed: U12.5 (IO4), U12.6 (IO4)
OTG_USB_D_N: J5.A7 (Dn1), J5.B7 (Dn2), U9.1 (IO1), U9.10 (IO1)
OTG_USB_D_P: J5.A6 (Dp1), J5.B6 (Dp2), U9.2 (IO2), U9.9 (IO2)
OTG_USB_VBUS: T6.3 (D)
OTG_VBUS: C62.2, J5.A4 (VBUS), J5.A9 (VBUS), J5.B4 (VBUS), J5.B9 (VBUS), R71.2, R72.1, U8.1 (IO1), U8.2 (IO2), U8.9 (IO2), U8.10 (IO1)
SHIELD: J9.Shell (Shield)
UART2_RX: R20.2
UART2_TX: R41.2
USB1_D_N: J11.A7 (Dn1), J11.B7 (Dn2)
USB1_D_P: J11.A6 (Dp1), J11.B6 (Dp2)
USBC_ADDR: IC7.22 (ADDR), TP21.1
USBC_FAULT: IC7.24 (VCONN_FAULT_N), TP32.1
USBC_ID: IC7.27 (ID), Q1.1 (G), R68.2, R101.1, TP18.1
USBC_INTN: IC7.23 (INT_N/OUT3), R67.1
USBC_SCL: IC7.26 (SCL/OUT2), R70.2
USBC_SDA: IC7.25 (SDA/OUT1), R69.2
USBC_VBUS: C35.2, J11.A4 (VBUS), J11.A9 (VBUS), J11.B4 (VBUS), J11.B9 (VBUS), L2.2, R42.2, R51.2, R131.2
USBSS_RX1_N: IC7.14 (RX1n), R104.1
USBSS_RX1_P: IC7.15 (RX1p), R106.1
USBSS_RX2_N: IC7.18 (RX2n), R109.1
USBSS_RX2_P: IC7.19 (RX2p), R110.1
USBSS_RX6_N: R108.1
USBSS_RX6_P: R107.1
USBSS_TX1_N: C48.2, IC7.16 (TX1n)
USBSS_TX1_P: C50.2, IC7.17 (TX1p)
USBSS_TX2_N: C53.2, IC7.20 (TX2n)
USBSS_TX2_P: C54.2, IC7.21 (TX2p)
USBSS_TX6_N: R105.1
USBSS_TX6_P: R103.1

Notes on the sheet:
Text
Debug USB connector
Debug UART
Current limit set to 2.1A
USB Load Switch
USB_PW
USB-OTG
USB-C Multiplexer
USB-C Connector
USB
